DaveBben/sunlight-glasses/firmware/src/ess.h

/*
 * Copyright (c) 2018 Nordic Semiconductor ASA
 * Copyright (c) 2016 Intel Corporation
 *
 * SPDX-License-Identifier: Apache-2.0
 */

#ifndef ZEPHYR_INCLUDE_BLUETOOTH_SERVICES_ESS_H_
#define ZEPHYR_INCLUDE_BLUETOOTH_SERVICES_ESS_H_

/**
 * @brief Environment Sensing Service (BAS)
 * @defgroup bt_bas Battery Service (BAS)
 * @ingroup bluetooth
 * @{
 *
 * [Experimental] Users should note that the APIs can change
 * as a part of ongoing development.
 */

#include <stdint.h>

#ifdef __cplusplus
extern "C" {
#endif

/** @brief Read light level value.
 *
 * Read the characteristic value of the battery level
 *
 *  @return The battery level in percent.
 */
int32_t bt_ess_get_light_level(void);

/** @brief Update battery level value.
 *
 * Update the characteristic value of the battery level
 * This will send a GATT notification to all current subscribers.
 *
 *  @param level The battery level in percent.
 *
 *  @return Zero in case of success and error code in case of error.
 */
int bt_ess_set_light_level(int32_t level);


#ifdef __cplusplus
}
#endif

/**
 * @}
 */

#endif /* ZEPHYR_INCLUDE_BLUETOOTH_SERVICES_BAS_H_ */
